Arya-070/EnviroGuard-AI/IMAGES/B.CU.png

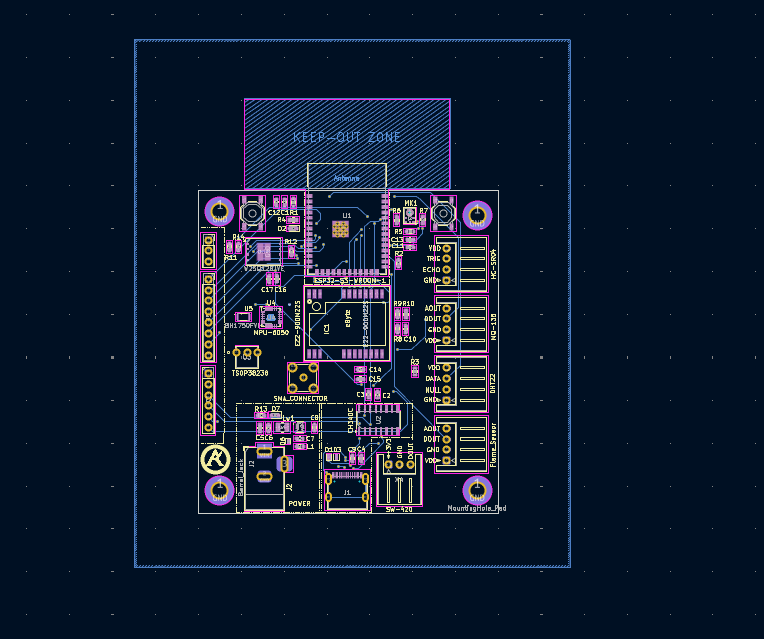
IMAGES/B.CU.png
