Arya-070/EnviroGuard-AI/IMAGES/EDITOR_VIEW.png

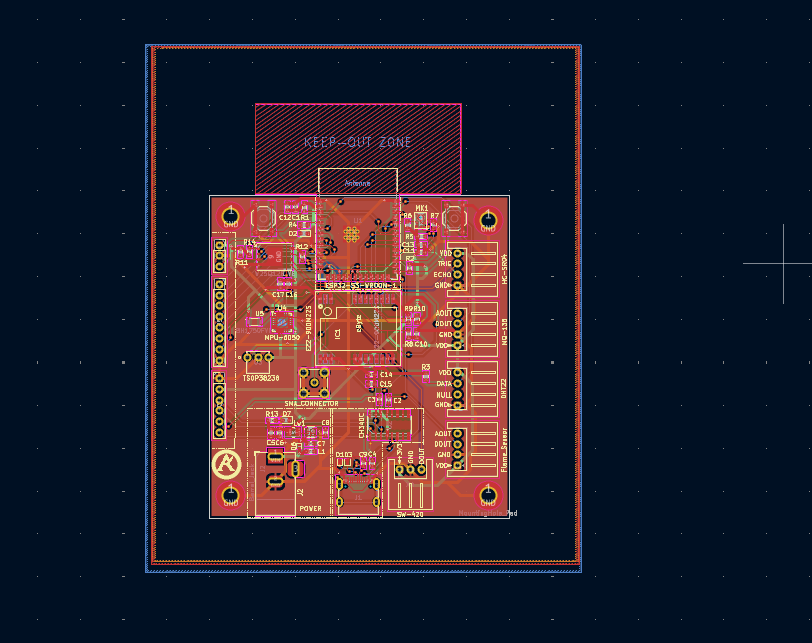
IMAGES/EDITOR_VIEW.png
