Arya-070/EnviroGuard-AI/IMAGES/In.1Cu.png

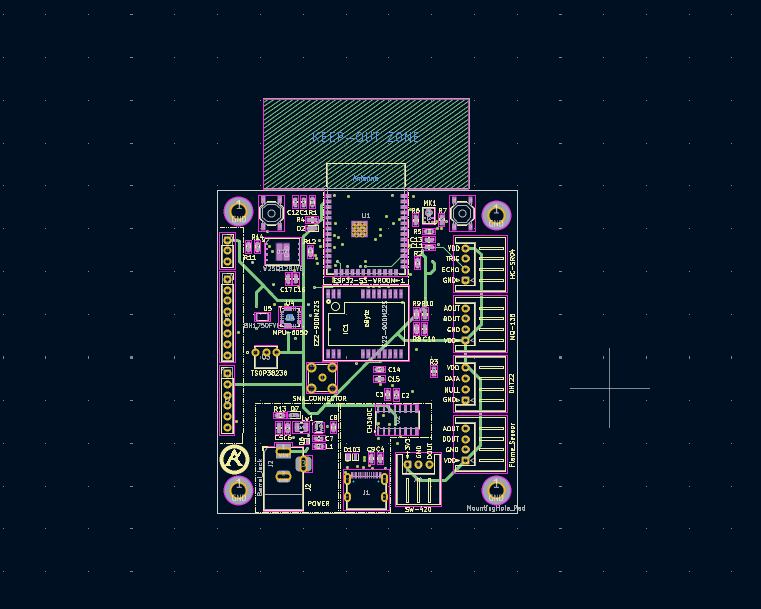
IMAGES/In.1Cu.png
