Arya-070/EnviroGuard-AI/IMAGES/In.2Cu.png

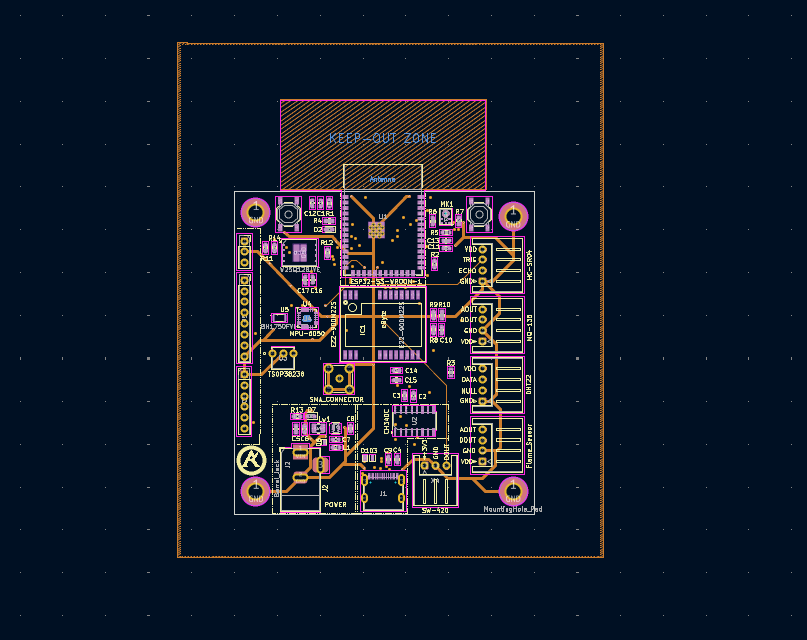
IMAGES/In.2Cu.png
