Arya-070/EnviroGuard-AI/IMAGES/SCH_AUDIO_INPUT.png

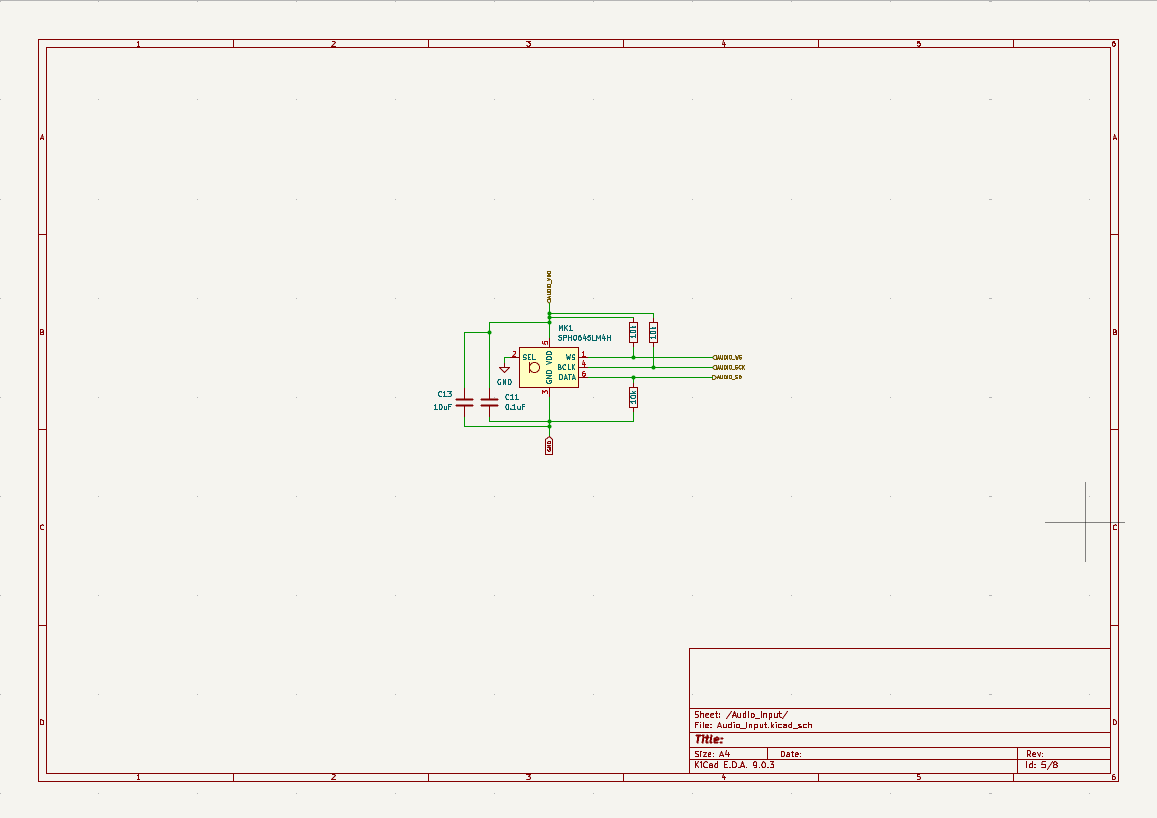
IMAGES/SCH_AUDIO_INPUT.png
