Arya-070/EnviroGuard-AI/IMAGES/SCH_COMMUNICATION.png

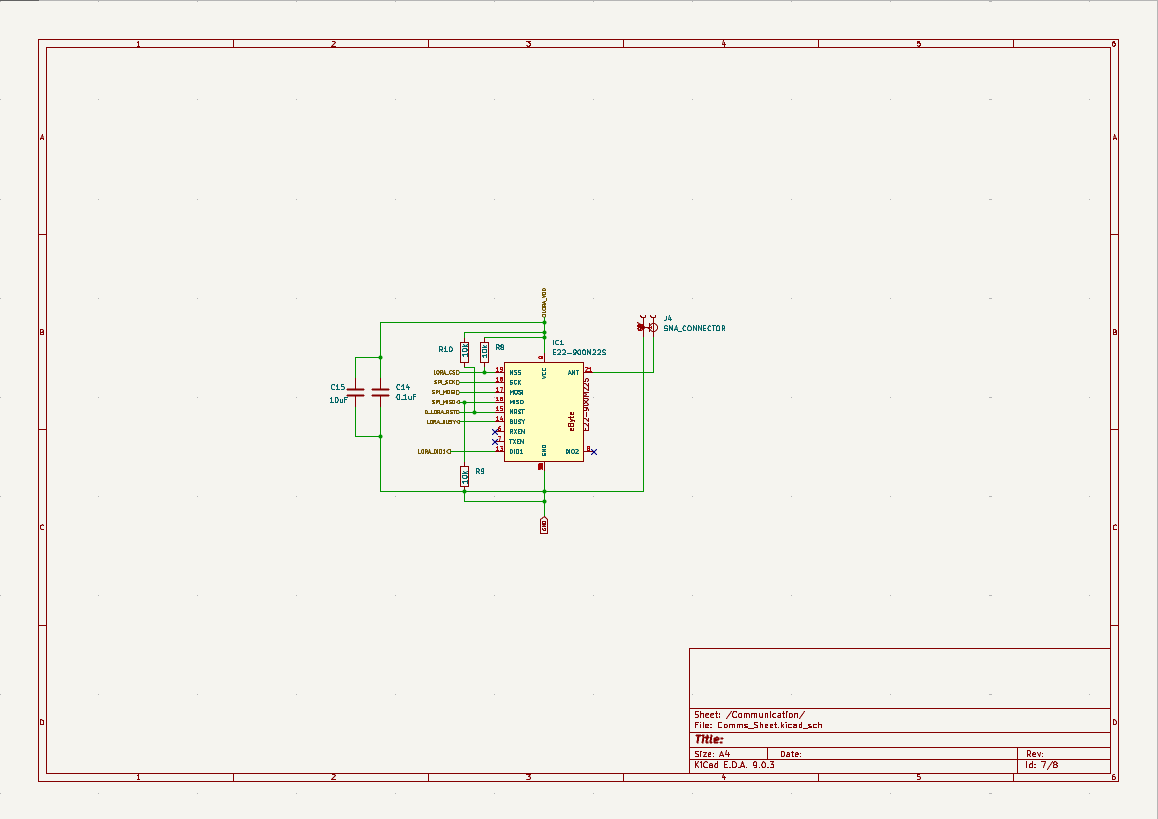
IMAGES/SCH_COMMUNICATION.png
