Arya-070/EnviroGuard-AI/IMAGES/SCH_ENV_SENSORS.png

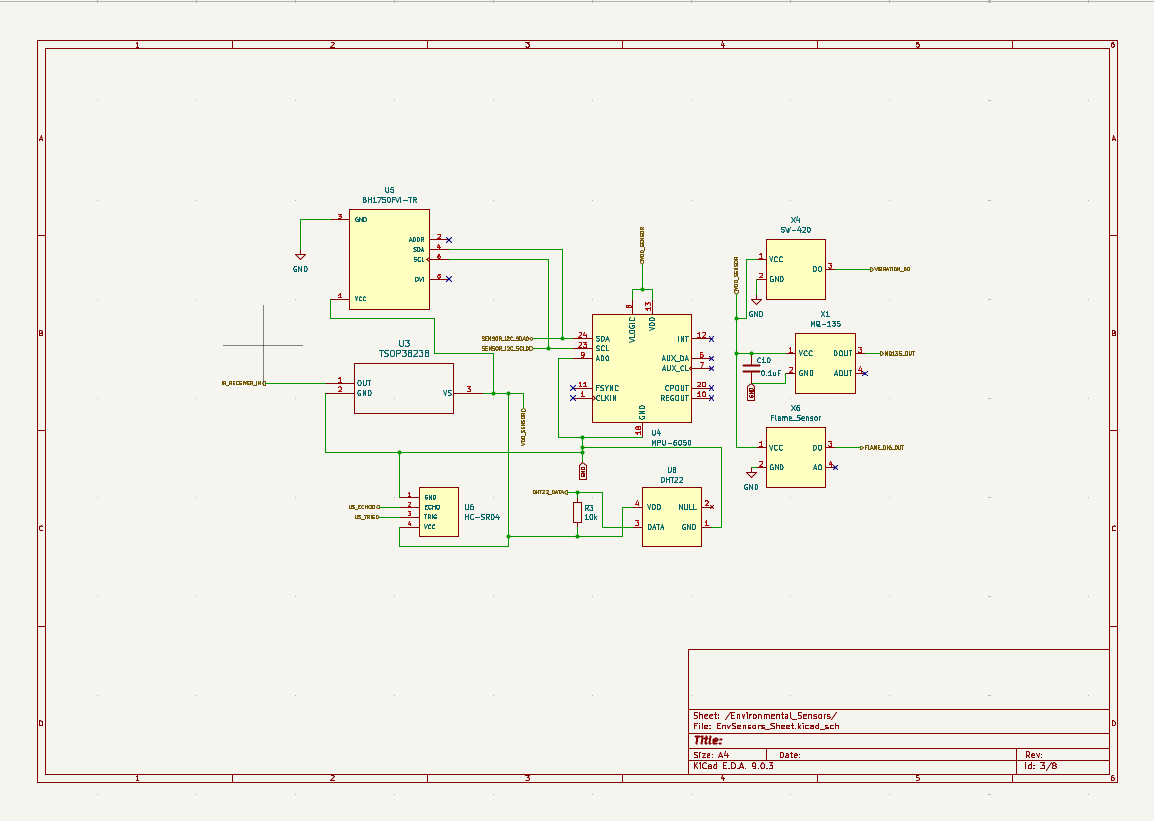
IMAGES/SCH_ENV_SENSORS.png
