Arya-070/EnviroGuard-AI/IMAGES/SCH_EXPANSION.png

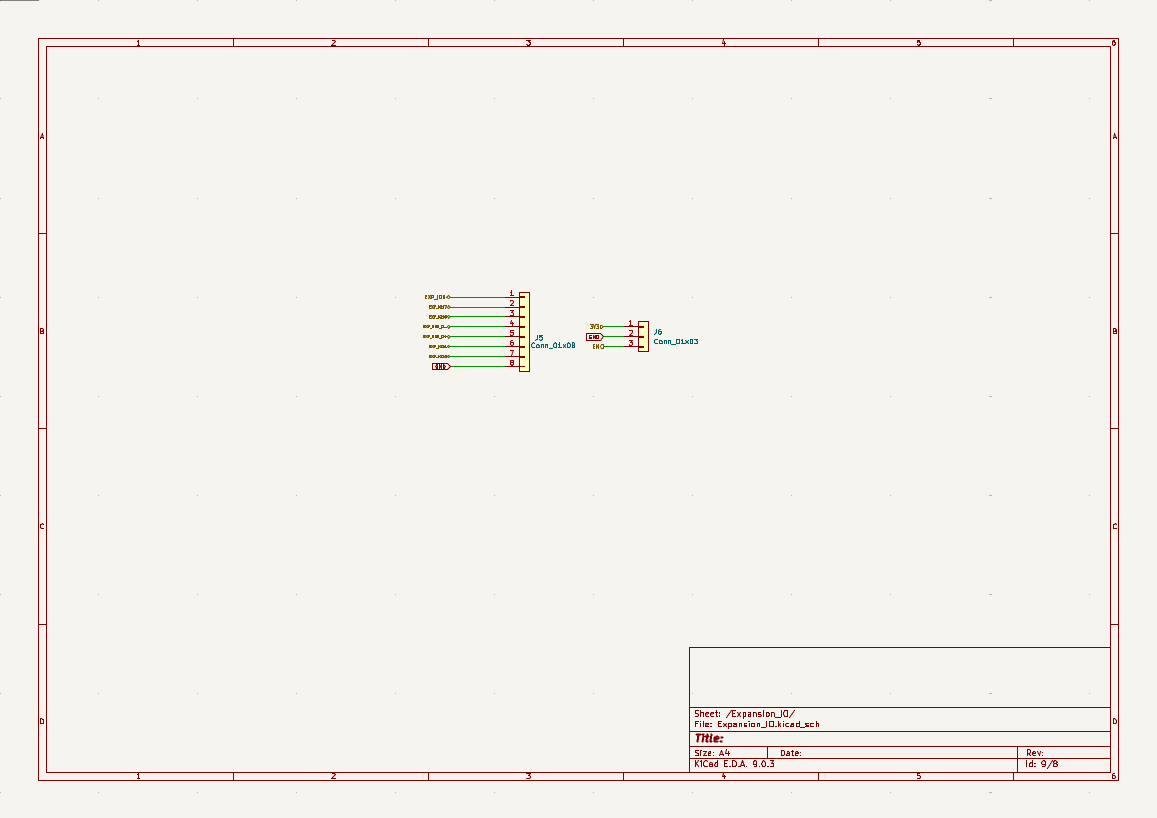
IMAGES/SCH_EXPANSION.png
