Arya-070/EnviroGuard-AI/IMAGES/SCH_POWER_MANAGEMENT.png

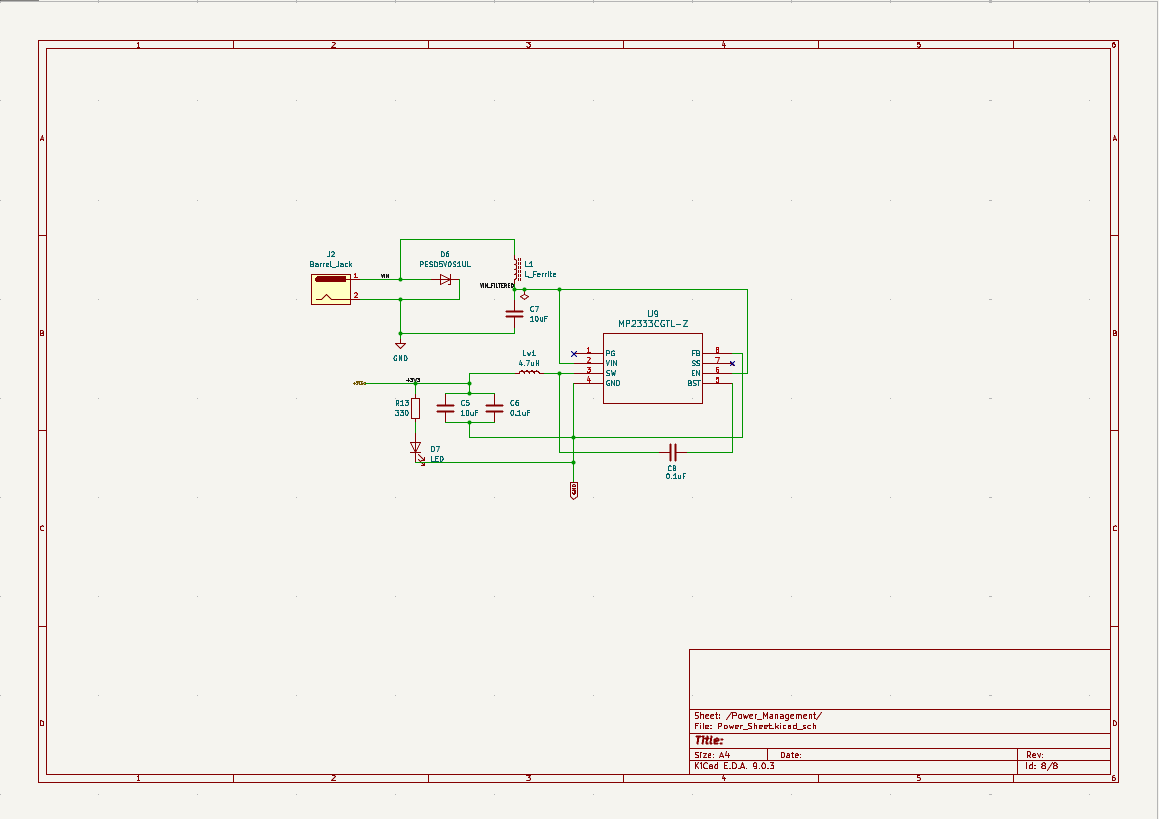
IMAGES/SCH_POWER_MANAGEMENT.png
